Rizz071/water-sentry/firmware/gateway/src/gpio_mapping.h

#ifndef GPIO_MAPPING_H
#define GPIO_MAPPING_H


#define BUZZER_PIN GPIO_NUM_0
#define LED_LINE_PIN GPIO_NUM_2
#define LINK_BUTTONS_PIN GPIO_NUM_1




#endif // GPIO_MAPPING_H
