Rizz071/water-sentry/firmware/sensor/src/link_button_handle.h

#ifndef LINK_BUTTON_HANDLE_H
#define LINK_BUTTON_HANDLE_H

#include "driver/gpio.h"
#include <stdint.h>

/**
 * @brief Инициализация кнопки привязки на датчике
 */
void link_button_init();

#endif // LINK_BUTTON_HANDLE_H
